whatnick/lantern_ring/docs/2022-05-01T04_47_43.136Z-ring-metallic_rect_bg.jpg

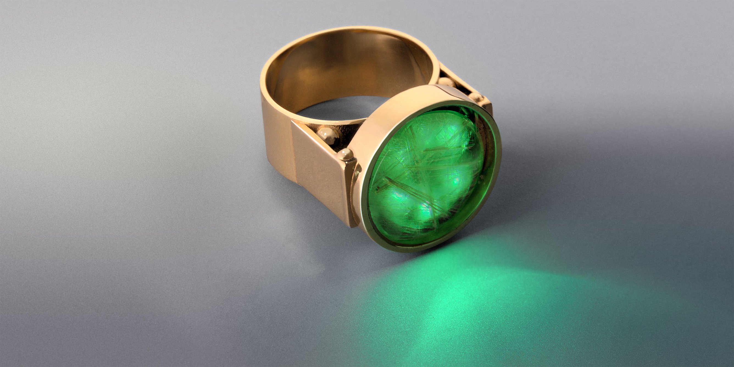
docs/2022-05-01T04_47_43.136Z-ring-metallic_rect_bg.jpg
