whatnick/lantern_ring/docs/bar_38.jpg

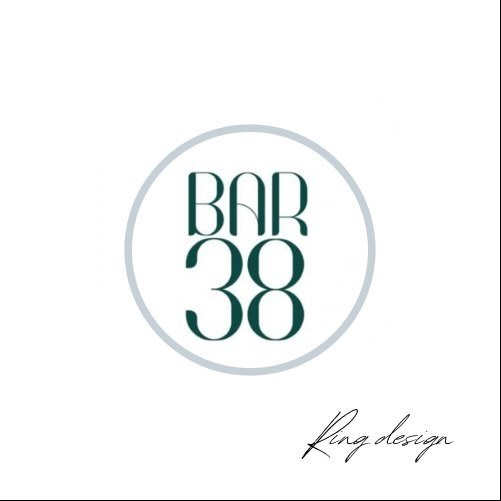
docs/bar_38.jpg
