whatnick/lantern_ring/docs/green-ring.jpg

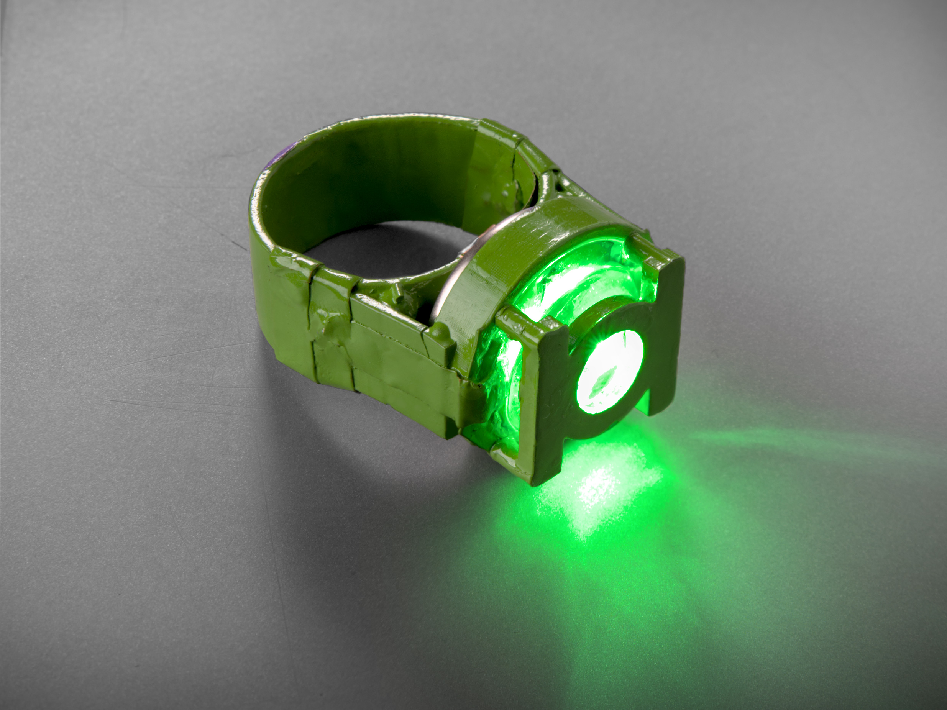
docs/green-ring.jpg
