whatnick/lantern_ring/docs/green_lantern.jpg

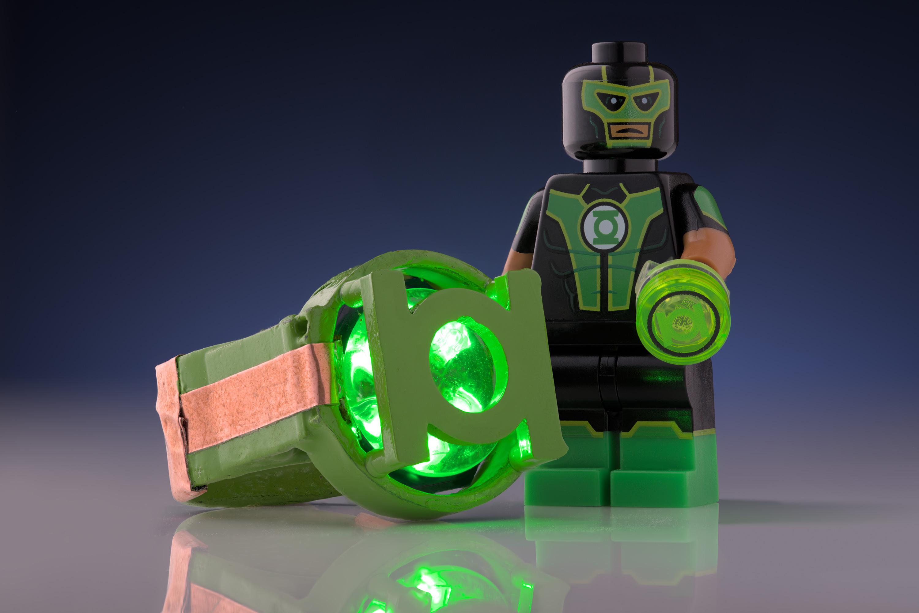
docs/green_lantern.jpg
