whatnick/lantern_ring/docs/magic_blue.jpg

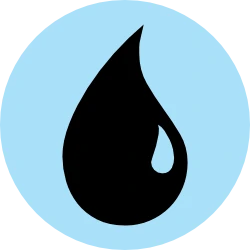
docs/magic_blue.jpg
