whatnick/lantern_ring/docs/magic_colourless.jpg

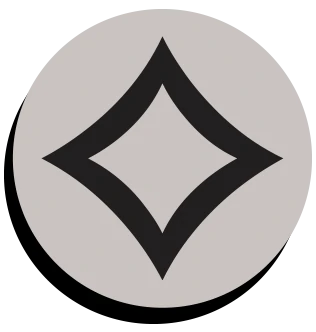
docs/magic_colourless.jpg
