whatnick/lantern_ring/docs/magic_green.jpg

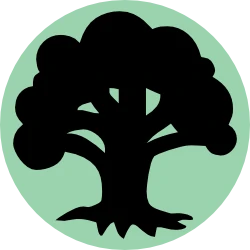
docs/magic_green.jpg
