whatnick/lantern_ring/docs/magic_green_cufflink_preview.png

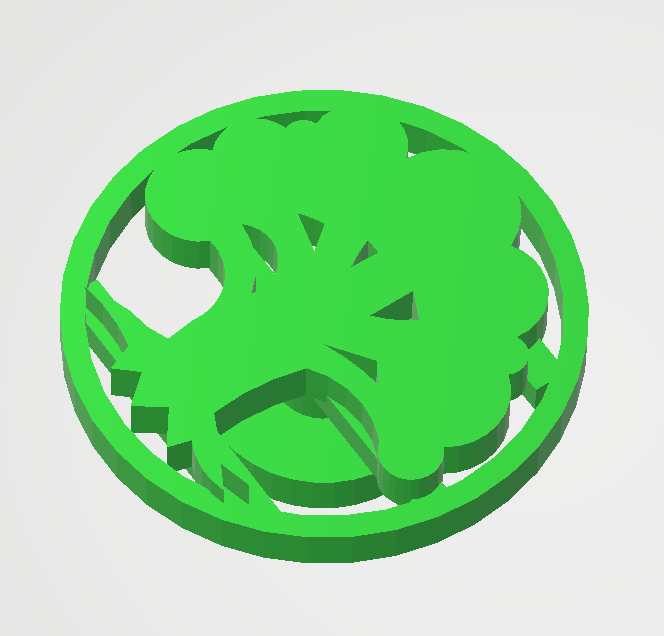
docs/magic_green_cufflink_preview.png
