whatnick/lantern_ring/docs/magic_red.jpg

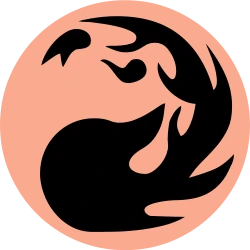
docs/magic_red.jpg
