whatnick/lantern_ring/docs/magic_white.jpg

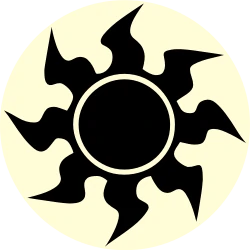
docs/magic_white.jpg
