whatnick/lantern_ring/docs/metallic_ring.jpg

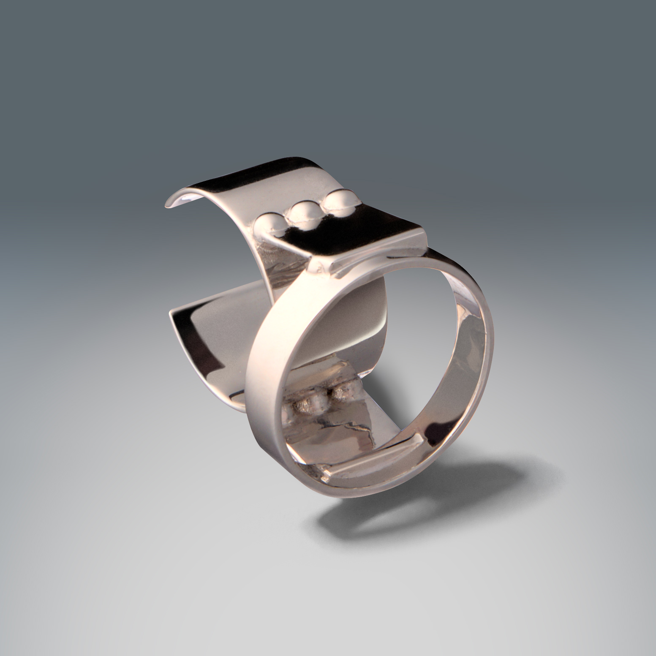
docs/metallic_ring.jpg
