whatnick/lantern_ring/docs/orange_ring.jpg

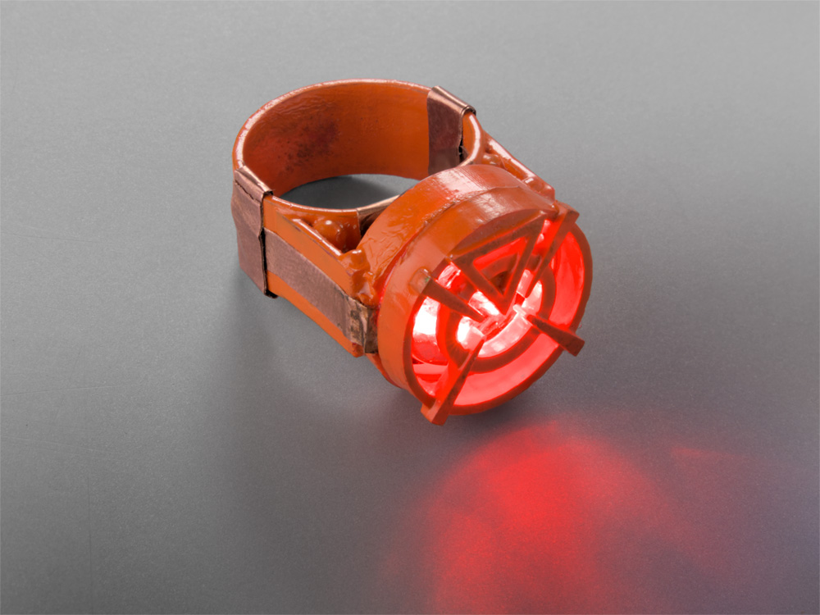
docs/orange_ring.jpg
