whatnick/lantern_ring/docs/pokemon_blue.jpg

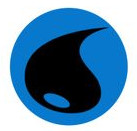
docs/pokemon_blue.jpg
