whatnick/lantern_ring/docs/pokemon_brown.jpg

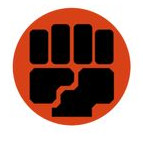
docs/pokemon_brown.jpg
