whatnick/lantern_ring/docs/pokemon_golden.jpg

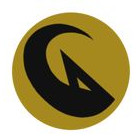
docs/pokemon_golden.jpg
