whatnick/lantern_ring/docs/pokemon_green.jpg

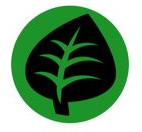
docs/pokemon_green.jpg
