whatnick/lantern_ring/docs/pokemon_grey.jpg

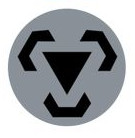
docs/pokemon_grey.jpg
