whatnick/lantern_ring/docs/pokemon_navy.jpg

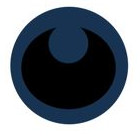
docs/pokemon_navy.jpg
