whatnick/lantern_ring/docs/pokemon_pins.jpg

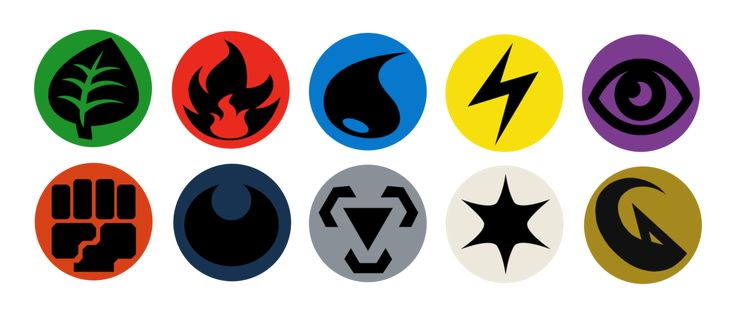
docs/pokemon_pins.jpg
