whatnick/lantern_ring/docs/pokemon_purple.jpg

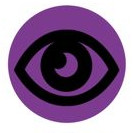
docs/pokemon_purple.jpg
