whatnick/lantern_ring/docs/pokemon_red.jpg

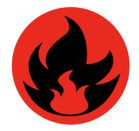
docs/pokemon_red.jpg
