whatnick/lantern_ring/docs/pokemon_white.jpg

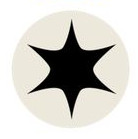
docs/pokemon_white.jpg
