whatnick/lantern_ring/docs/pokemon_yellow.jpg

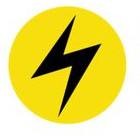
docs/pokemon_yellow.jpg
