whatnick/lantern_ring/docs/ptcg_green.png

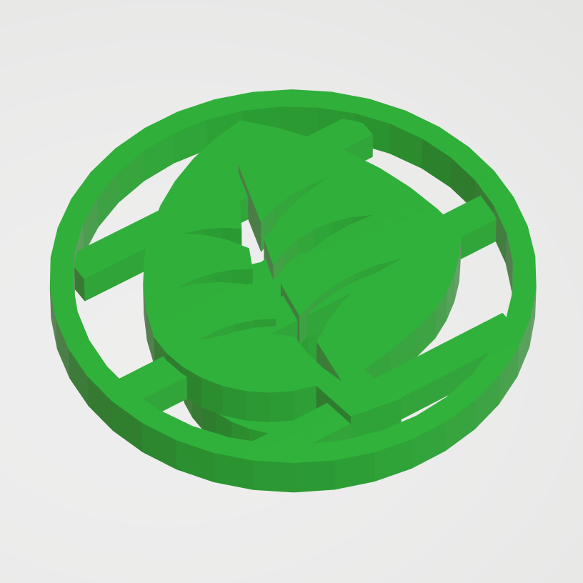
docs/ptcg_green.png
