whatnick/lantern_ring/docs/purple_ring.jpg

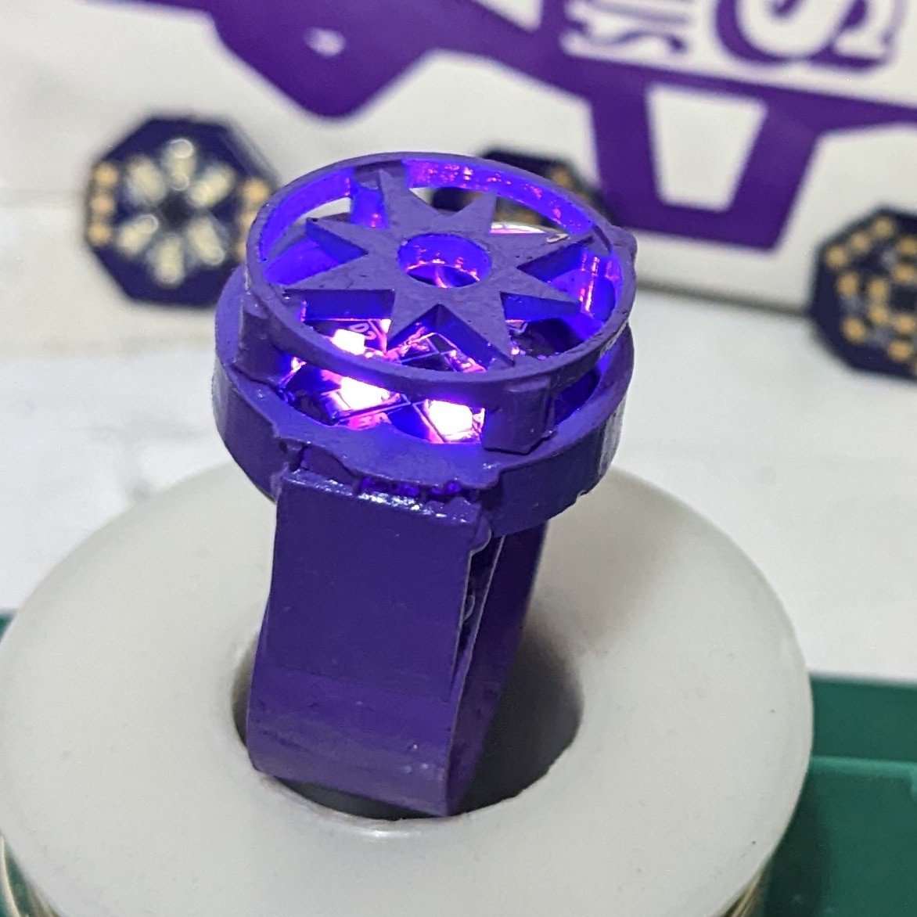
docs/purple_ring.jpg
