whatnick/lantern_ring/docs/ring-ice-blue.jpg

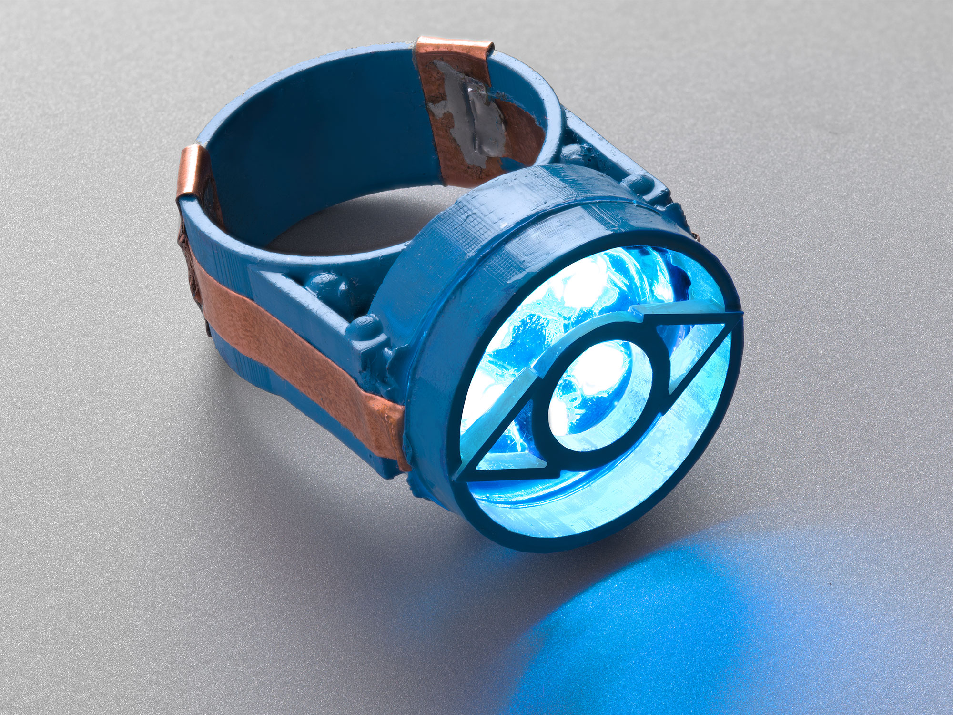
docs/ring-ice-blue.jpg
