whatnick/lantern_ring/docs/ring-white.jpg

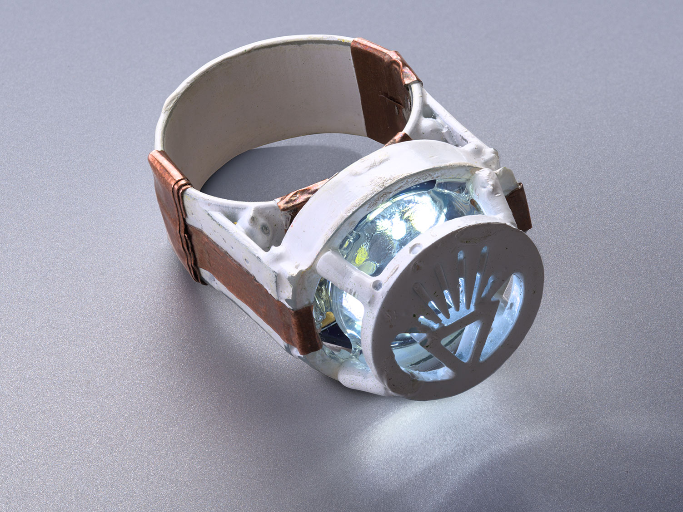
docs/ring-white.jpg
