whatnick/lantern_ring/docs/ring_and_cats_eye.jpg

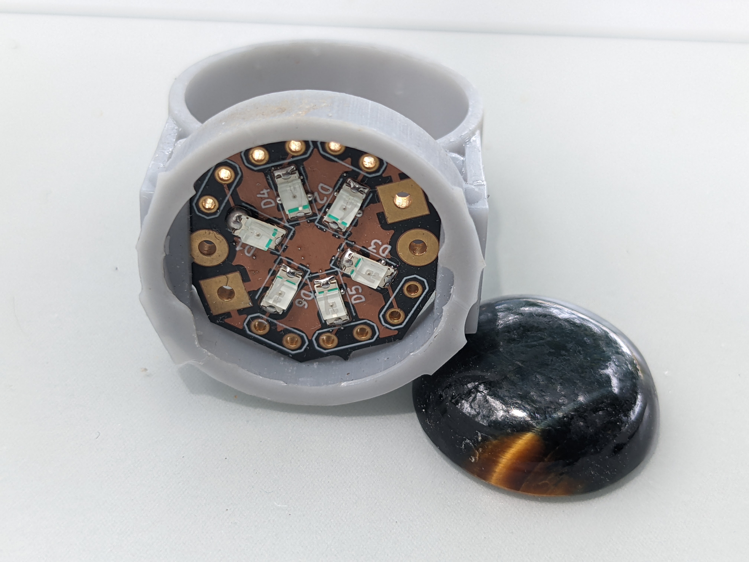
docs/ring_and_cats_eye.jpg
