whatnick/lantern_ring/docs/ring_pcb.PNG

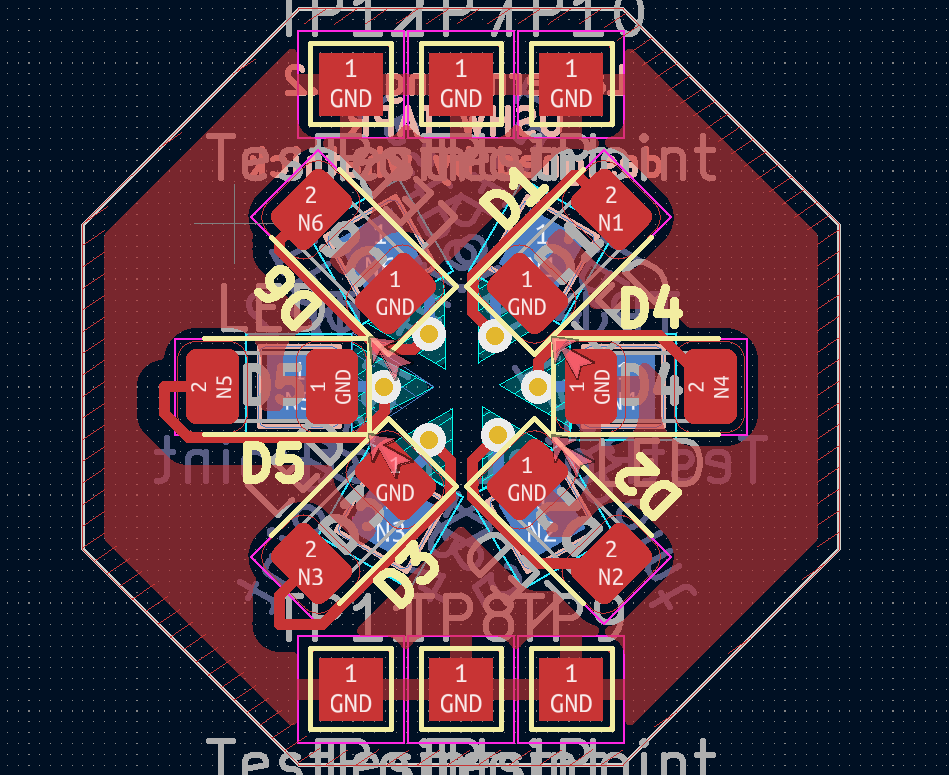
docs/ring_pcb.PNG
