whatnick/lantern_ring/docs/ring_pcb_3d.PNG

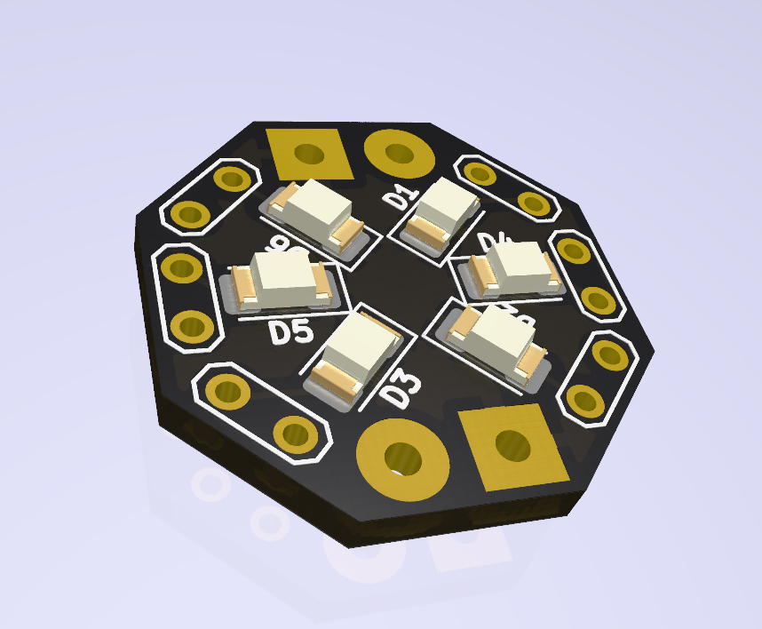
docs/ring_pcb_3d.PNG
