whatnick/lantern_ring/docs/ring_selection.jpg

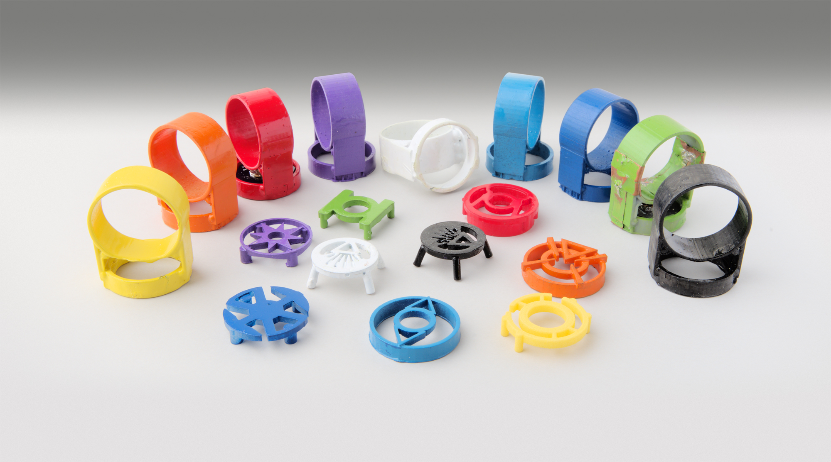
docs/ring_selection.jpg
