whatnick/lantern_ring/docs/shapeways_mana_cufflinks.png

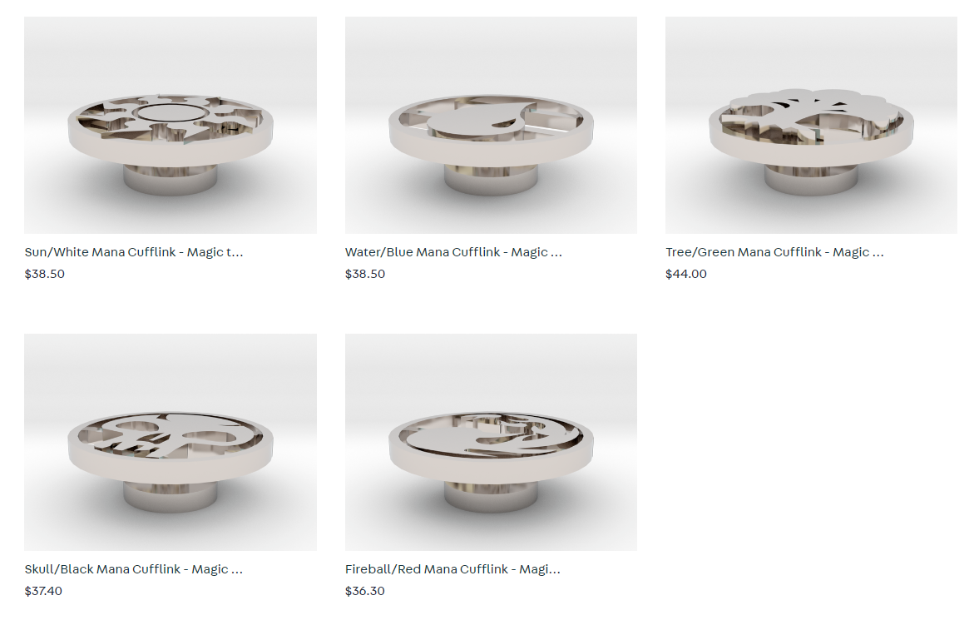
docs/shapeways_mana_cufflinks.png
