whatnick/lantern_ring/docs/tv_b_gone.png

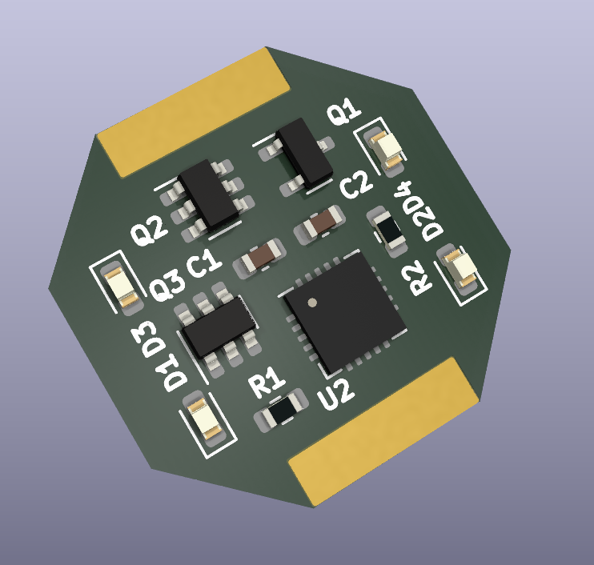
docs/tv_b_gone.png
