whatnick/lantern_ring/docs/yellow_ring.jpg

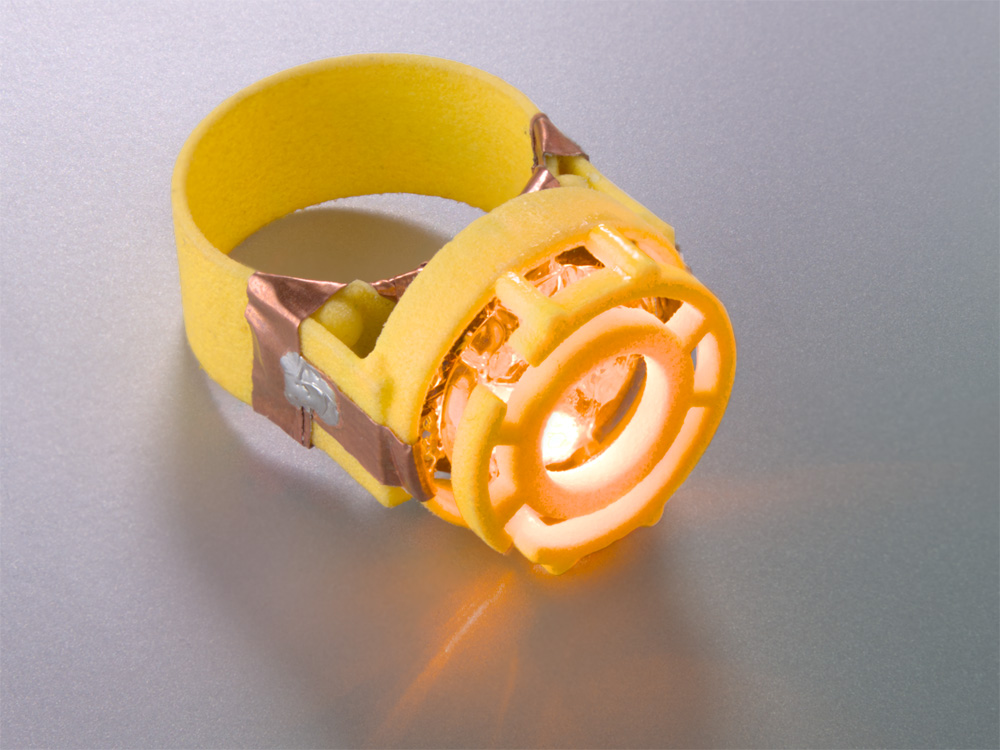
docs/yellow_ring.jpg
