whatnick/lantern_ring/hardware/v2.0/ring_ir_prog_clip/generated/ring_ir_prog_fence_bottom.png

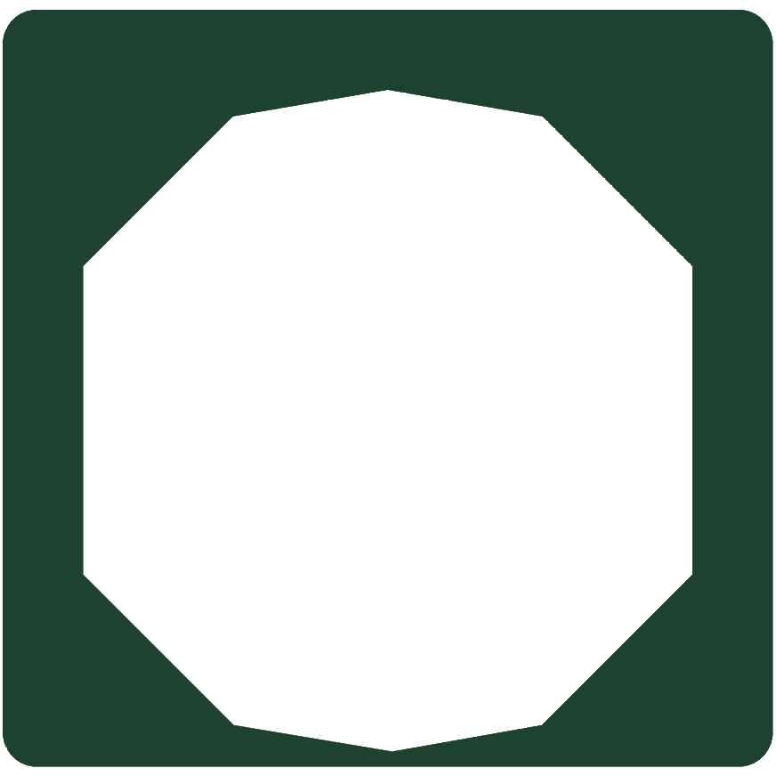
hardware/v2.0/ring_ir_prog_clip/generated/ring_ir_prog_fence_bottom.png
